cheng3100/wifi_extension_touch_screen/doc/pic/real_effect_2.png

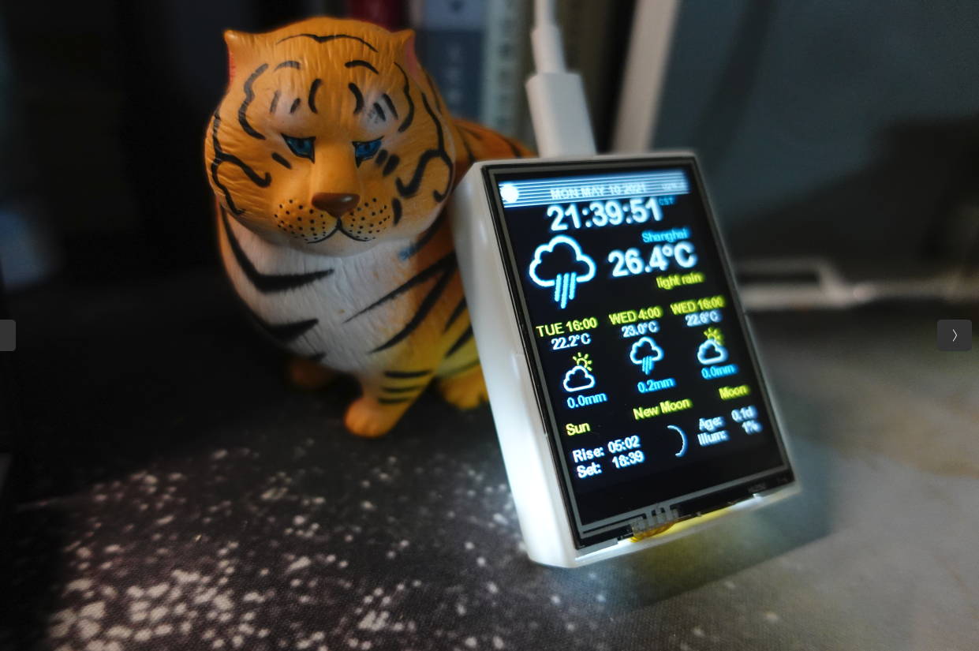
doc/pic/real_effect_2.png
