cheng3100/wifi_extension_touch_screen/software/main/src/weather/src/OpenWeatherMapCurrent.cpp

/**The MIT License (MIT)
 
 Copyright (c) 2018 by ThingPulse Ltd., https://thingpulse.com
 
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
 THE SOFTWARE IS PROVIDED "AS IS", WITHOUT WARRANTY OF ANY KIND, EXPRESS OR
 IMPLIED, INCLUDING BUT NOT LIMITED TO THE WARRANTIES OF MERCHANTABILITY,
 FITNESS FOR A PARTICULAR PURPOSE AND NONINFRINGEMENT. IN NO EVENT SHALL THE
 AUTHORS OR COPYRIGHT HOLDERS BE LIABLE FOR ANY CLAIM, DAMAGES OR OTHER
 LIABILITY, WHETHER IN AN ACTION OF CONTRACT, TORT OR OTHERWISE, ARISING FROM,
 OUT OF OR IN CONNECTION WITH THE SOFTWARE OR THE USE OR OTHER DEALINGS IN THE
 SOFTWARE.
 */

#include "ESPWiFi.h"
#include <WiFiClient.h>
#include "OpenWeatherMapCurrent.h"

OpenWeatherMapCurrent::OpenWeatherMapCurrent() {

}

void OpenWeatherMapCurrent::updateCurrent(OpenWeatherMapCurrentData *data, String appId, String location) {
  doUpdate(data, buildPath(appId, "q=" + location));
}

void OpenWeatherMapCurrent::updateCurrentById(OpenWeatherMapCurrentData *data, String appId, String locationId) {
  doUpdate(data, buildPath(appId, "id=" + locationId));
}

String OpenWeatherMapCurrent::buildPath(String appId, String locationParameter) {
  String units = metric ? "metric" : "imperial";
  return "/data/2.5/weather?" + locationParameter + "&appid=" + appId + "&units=" + units + "&lang=" + language;
}

void OpenWeatherMapCurrent::doUpdate(OpenWeatherMapCurrentData *data, String path) {
  unsigned long lostTest = 10000UL;
  unsigned long lost_do = millis();
  this->weatherItemCounter = 0;
  this->data = data;
  JsonStreamingParser parser;
  parser.setListener(this);
  Serial.printf("[HTTP] Requesting resource at http://%s:%u%s\n", host.c_str(), port, path.c_str());

  WiFiClient client;
  if(client.connect(host, port)) {
    bool isBody = false;
    char c;
    Serial.println("[HTTP] connected, now GETting data");
    client.print("GET " + path + " HTTP/1.1\r\n"
                 "Host: " + host + "\r\n"
                 "Connection: close\r\n\r\n");

    while (client.connected() || client.available()) {
      if (client.available()) {
		if ((millis() - lost_do) > lostTest) {
		  Serial.println("[HTTP] lost in client with a timeout" \
				  "remain last update");
		  client.stop();
		  return;
		  // ESP.restart();
		}
        c = client.read();
        if (c == '{' || c == '[') {
          isBody = true;
        }
        if (isBody) {
          parser.parse(c);
        }
      }
      // give WiFi and TCP/IP libraries a chance to handle pending events
      yield();
    }
    client.stop();
  } else {
    Serial.println("[HTTP] failed to connect to host");
  }
  this->data = nullptr;
}

void OpenWeatherMapCurrent::whitespace(char c) {
  Serial.println("whitespace");
}

void OpenWeatherMapCurrent::startDocument() {
  Serial.println("start document");
}

void OpenWeatherMapCurrent::key(String key) {
  currentKey = String(key);
}

void OpenWeatherMapCurrent::value(String value) {
  // "lon": 8.54, float lon;
  if (currentKey == "lon") {
    this->data->lon = value.toFloat();
  }
  // "lat": 47.37 float lat;
  if (currentKey == "lat") {
    this->data->lat = value.toFloat();
  }
  // weatherItemCounter: only get the first item if more than one is available
  if (currentParent == "weather" && weatherItemCounter == 0) {
    // "id": 521, weatherId weatherId;
    if (currentKey == "id") {
      this->data->weatherId = value.toInt();
    }
    // "main": "Rain", String main;
    if (currentKey == "main") {
      this->data->main = value;
    }
    // "description": "shower rain", String description;
    if (currentKey == "description") {
      this->data->description = value;
    }
    // "icon": "09d" String icon;
   //String iconMeteoCon;
    if (currentKey == "icon") {
      this->data->icon = value;
      this->data->iconMeteoCon = getMeteoconIcon(value);
    }

  }

  // "temp": 290.56, float temp;
  if (currentKey == "temp") {
    this->data->temp = value.toFloat();
  }
  // "pressure": 1013, uint16_t pressure;
  if (currentKey == "pressure") {
    this->data->pressure = value.toInt();
  }
  // "humidity": 87, uint8_t humidity;
  if (currentKey == "humidity") {
    this->data->humidity = value.toInt();
  }
  // "temp_min": 289.15, float tempMin;
  if (currentKey == "temp_min") {
    this->data->tempMin = value.toFloat();
  }
  // "temp_max": 292.15 float tempMax;
  if (currentKey == "temp_max") {
    this->data->tempMax = value.toFloat();
  }
  // visibility: 10000, uint16_t visibility;
  if (currentKey == "visibility") {
    this->data->visibility = value.toInt();
  }
  // "wind": {"speed": 1.5}, float windSpeed;
  if (currentKey == "speed") {
    this->data->windSpeed = value.toFloat();
  }
  // "wind": {deg: 226.505}, float windDeg;
  if (currentKey == "deg") {
    this->data->windDeg = value.toFloat();
  }
  // "clouds": {"all": 90}, uint8_t clouds;
  if (currentKey == "all") {
    this->data->clouds = value.toInt();
  }
  // "dt": 1527015000, uint64_t observationTime;
  if (currentKey == "dt") {
    this->data->observationTime = value.toInt();
  }
  // "country": "CH", String country;
  if (currentKey == "country") {
    this->data->country = value;
  }
  // "sunrise": 1526960448, uint32_t sunrise;
  if (currentKey == "sunrise") {
    this->data->sunrise = value.toInt();
  }
  // "sunset": 1527015901 uint32_t sunset;
  if (currentKey == "sunset") {
    this->data->sunset = value.toInt();
  }
  // "name": "Zurich", String cityName;
  if (currentKey == "name") {
    this->data->cityName = value;
  }
}

void OpenWeatherMapCurrent::endArray() {

}


void OpenWeatherMapCurrent::startObject() {
  currentParent = currentKey;
}

void OpenWeatherMapCurrent::endObject() {
  if (currentParent == "weather") {
    weatherItemCounter++;
  }
  currentParent = "";
}

void OpenWeatherMapCurrent::endDocument() {
	Serial.println("End document");
}

void OpenWeatherMapCurrent::startArray() {

}


String OpenWeatherMapCurrent::getMeteoconIcon(String icon) {
 	// clear sky
  // 01d
  if (icon == "01d") 	{
    return "B";
  }
  // 01n
  if (icon == "01n") 	{
    return "C";
  }
  // few clouds
  // 02d
  if (icon == "02d") 	{
    return "H";
  }
  // 02n
  if (icon == "02n") 	{
    return "4";
  }
  // scattered clouds
  // 03d
  if (icon == "03d") 	{
    return "N";
  }
  // 03n
  if (icon == "03n") 	{
    return "5";
  }
  // broken clouds
  // 04d
  if (icon == "04d") 	{
    return "Y";
  }
  // 04n
  if (icon == "04n") 	{
    return "%";
  }
  // shower rain
  // 09d
  if (icon == "09d") 	{
    return "R";
  }
  // 09n
  if (icon == "09n") 	{
    return "8";
  }
  // rain
  // 10d
  if (icon == "10d") 	{
    return "Q";
  }
  // 10n
  if (icon == "10n") 	{
    return "7";
  }
  // thunderstorm
  // 11d
  if (icon == "11d") 	{
    return "P";
  }
  // 11n
  if (icon == "11n") 	{
    return "6";
  }
  // snow
  // 13d
  if (icon == "13d") 	{
    return "W";
  }
  // 13n
  if (icon == "13n") 	{
    return "#";
  }
  // mist
  // 50d
  if (icon == "50d") 	{
    return "M";
  }
  // 50n
  if (icon == "50n") 	{
    return "M";
  }
  // Nothing matched: N/A
  return ")";

}
