cheng3100/wifi_extension_touch_screen/software/main/webfiles.h

#ifndef webfiles_h
#define webfiles_h

// comment that out if you want to save program memory and know how to upload the web files to the SPIFFS manually
#define USE_PROGMEM_WEB_FILES 

#ifdef USE_PROGMEM_WEB_FILES
const char attackhtml[] PROGMEM = {0x1f, 0x8b, 0x08, 0x08, 0x1b, 0xc8, 0xb5, 0x60, 0x02, 0xff, 0x61, 0x74, 0x74, 0x61, 0x63, 0x6b, 0x2e, 0x68, 0x74, 0x6d, 0x6c, 0x00, 0xa5, 0x57, 0xdb, 0x6e, 0xdb, 0x38, 0x10, 0xfd, 0x95, 0x89, 0xf7, 0xa1, 0x5d, 0xa0, 0xb6, 0x12, 0x17, 0x08, 0xd2, 0xc0, 0x16, 0xd0, 0x2b, 0x10, 0xa0, 0xdb, 0x06, 0x1b, 0x77, 0x8b, 0x7d, 0x0a, 0x68, 0x89, 0xb6, 0x58, 0xd3, 0xa4, 0x4a, 0x52, 0x71, 0x0d, 0xec, 0xc7, 0xef, 0x19, 0x92, 0x72, 0x6d, 0xc7, 0x41, 0x1f, 0x0a, 0x04, 0x8a, 0x4c, 0xce, 0x70, 0xce, 0xdc, 0x0e, 0x47, 0x93, 0xb3, 0xe1, 0x70, 0x48, 0xb3, 0x46, 0x79, 0xf2, 0x76, 0x11, 0x36, 0xc2, 0x49, 0xc2, 0xbb, 0x56, 0x95, 0x34, 0x5e, 0xd6, 0xd4, 0x99, 0x5a, 0x3a, 0x0a, 0x8d, 0xa4, 0xbf, 0x6e, 0x66, 0xf4, 0x31, 0x2d, 0x5f, 0x53, 0x13, 0x42, 0xeb, 0xaf, 0x8b, 0x62, 0xa9, 0x42, 0xd3, 0xcd, 0x47, 0x95, 0x5d, 0x17, 0xbe, 0x15, 0x95, 0x6c, 0xba, 0xc6, 0x04, 0x59, 0x35, 0x85, 0xf4, 0xed, 0xd5, 0xf8, 0xf2, 0xf2, 0xbe, 0x96, 0xa2, 0x83, 0xb6, 0xa3, 0xe1, 0xb0, 0xa4, 0xc9, 0xd9, 0x3b, 0x5b, 0x85, 0x6d, 0x2b, 0xa1, 0xbf, 0xd6, 0xf8, 0xbd, 0x96, 0x41, 0x50, 0xd5, 0x08, 0xe7, 0x65, 0x98, 0x7e, 0x99, 0x7d, 0x18, 0x5e, 0x51, 0xbf, 0x6a, 0xc4, 0x5a, 0x4e, 0x1f, 0x94, 0xdc, 0xb4, 0xd6, 0x05, 0xa2, 0xca, 0xe2, 0x5c, 0x13, 0xa6, 0x83, 0x8d, 0xaa, 0x43, 0x33, 0xad, 0xe5, 0x03, 0xa0, 0x0c, 0xe3, 0x8f, 0x17, 0xa4, 0x8c, 0x0a, 0x4a, 0xe8, 0xa1, 0xaf, 0x84, 0x96, 0xd3, 0xf3, 0xd1, 0xd5, 0x0b, 0x5a, 0x63, 0x6d, 0x8d, 0xa5, 0x4e, 0x0d, 0x0e, 0x4e, 0x04, 0x96, 0xb5, 0x1c, 0x56, 0x56, 0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
xb4, 0xcd, 0xe0, 0xfe, 0x07, 0x53, 0x5d, 0xd3, 0x82, 0xe3, 0x0d, 0x00, 0x00};
const char infohtml[] PROGMEM = {0x1f, 0x8b, 0x08, 0x08, 0x1b, 0xc8, 0xb5, 0x60, 0x02, 0xff, 0x69, 0x6e, 0x66, 0x6f, 0x2e, 0x68, 0x74, 0x6d, 0x6c, 0x00, 0x9d, 0x58, 0x6b, 0x6f, 0xdb, 0x3a, 0x12, 0xfd, 0x2b, 0x53, 0xef, 0x87, 0x6d, 0x01, 0x3f, 0xf2, 0x00, 0x82, 0xde, 0xc2, 0x31, 0x56, 0x8d, 0x95, 0x46, 0x5b, 0xc7, 0x36, 0x6c, 0xa7, 0xd9, 0x7e, 0x2a, 0x68, 0x89, 0xb6, 0xd8, 0xc8, 0xa4, 0xae, 0x48, 0xd9, 0xf1, 0xc5, 0xfe, 0xf8, 0x3d, 0x43, 0xc9, 0x8f, 0xc4, 0xed, 0x22, 0xbb, 0x40, 0x60, 0x9b, 0xe4, 0xcc, 0x99, 0xe1, 0xbc, 0x99, 0xee, 0xbb, 0x56, 0xab, 0x45, 0xb3, 0x54, 0x59, 0xb2, 0x66, 0xe1, 0x36, 0xa2, 0x90, 0x84, 0xdf, 0x99, 0x8a, 0xa5, 0xb6, 0x32, 0xa1, 0x52, 0x27, 0xb2, 0x20, 0x97, 0x4a, 0xba, 0x8f, 0x66, 0x34, 0xa8, 0xb6, 0x3f, 0x51, 0xea, 0x5c, 0x6e, 0x3f, 0x75, 0x3a, 0x4b, 0xe5, 0xd2, 0x72, 0xde, 0x8e, 0xcd, 0xaa, 0x63, 0x73, 0x11, 0xcb, 0xb4, 0x4c, 0xb5, 0x93, 0x71, 0xda, 0x91, 0x36, 0xff, 0x78, 0x71, 0x75, 0xf5, 0x23, 0x91, 0xa2, 0x04, 0x77, 0x41, 0xad, 0x56, 0x8f, 0xba, 0xef, 0xfa, 0x26, 0x76, 0xdb, 0x5c, 0x82, 0x7f, 0x95, 0x61, 0xbd, 0x92, 0x4e, 0x50, 0x9c, 0x8a, 0xc2, 0x4a, 0x77, 0xfd, 0x30, 0xbb, 0x6d, 0x7d, 0xa4, 0xdd, 0xae, 0x16, 0x2b, 0x79, 0xbd, 0x56, 0x72, 0x93, 0x9b, 0xc2, 0x11, 0xc5, 0x06, 0xb8, 0xda, 0x5d, 0x37, 0x36, 0x2a, 0x71, 0xe9, 0x75, 0x22, 0xd7, 0x50, 0xa5, 0xe5, 0x17, 0x4d, 0x52, 0x5a, 0x39, 0x25, 0xb2, 0x96, 0x8d, 0x45, 0x26, 0xaf, 0xcf, 0xda, 0x1f, 0x9b, 0xb4, 0xc2, 0xde, 0x0a, 0x5b, 0xa5, 0x6a, 0xbc, 0x40, 0x84, 0x2e, 0x2b, 0xd9, 0x8a, 0x4d, 0x6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
2, 0x23, 0x20, 0xe1, 0xf5, 0xc3, 0x34, 0x3c, 0xe8, 0xd2, 0x0f, 0x83, 0x01, 0xb0, 0xa6, 0xcc, 0x7c, 0x4c, 0xdc, 0xae, 0xeb, 0x52, 0xfd, 0x9a, 0x7d, 0xf9, 0xb5, 0x30, 0x06, 0x03, 0x30, 0xff, 0x1f, 0x21, 0x47, 0x45, 0xc3, 0xe3, 0x17, 0x2d, 0xdd, 0x47, 0x56, 0xef, 0x5b, 0xfd, 0xe3, 0xa2, 0x7d, 0xd5, 0x3e, 0xeb, 0xf2, 0x8c, 0xaa, 0xeb, 0xd8, 0x38, 0x1d, 0x7d, 0x51, 0xe4, 0x77, 0xd3, 0x6a, 0x7b, 0x25, 0x32, 0x57, 0x60, 0x5e, 0x8c, 0x2d, 0x57, 0xfc, 0x93, 0x02, 0xff, 0xa8, 0x9e, 0x94, 0x2f, 0xef, 0xff, 0xde, 0x43, 0xf0, 0x38, 0x56, 0xbd, 0xda, 0x0f, 0xaf, 0x63, 0x5f, 0xff, 0x6b, 0xe5, 0xfe, 0x03, 0x03, 0xc2, 0x59, 0xa3, 0x7f, 0x12, 0x00, 0x00};
const char settingshtml[] PROGMEM = {0x1f, 0x8b, 0x08, 0x08, 0x1b, 0xc8, 0xb5, 0x60, 0x02, 0xff, 0x73, 0x65, 0x74, 0x74, 0x69, 0x6e, 0x67, 0x73, 0x2e, 0x68, 0x74, 0x6d, 0x6c, 0x00, 0x95, 0x55, 0x6d, 0x6f, 0xdb, 0x36, 0x10, 0xfe, 0x2b, 0x57, 0xed, 0x43, 0x12, 0x20, 0x92, 0x9a, 0x04, 0x08, 0xd2, 0x44, 0xd2, 0x30, 0x34, 0x0d, 0x10, 0x20, 0xdd, 0x8a, 0x26, 0xdb, 0x3e, 0x06, 0x34, 0x75, 0xb6, 0x58, 0x53, 0xa4, 0x46, 0x9e, 0xec, 0x06, 0xd8, 0x8f, 0xdf, 0x9d, 0x24, 0xe7, 0xc5, 0x71, 0x8a, 0xee, 0x83, 0x29, 0xfa, 0x78, 0x6f, 0xcf, 0xdd, 0xf1, 0x61, 0xf1, 0x2e, 0x4d, 0x53, 0xb8, 0x6b, 0x4c, 0x84, 0xe8, 0xe7, 0xb4, 0x56, 0x01, 0x81, 0xf7, 0xd6, 0x68, 0x74, 0x11, 0x6b, 0xe8, 0x5d, 0x8d, 0x01, 0xa8, 0x41, 0xf8, 0x7c, 0x7d, 0x07, 0x37, 0xa3, 0xf8, 0x1c, 0x1a, 0xa2, 0x2e, 0x9e, 0xe7, 0xf9, 0xc2, 0x50, 0xd3, 0xcf, 0x32, 0xed, 0xdb, 0x3c, 0x76, 0x4a, 0x63, 0xd3, 0x37, 0x8e, 0x50, 0x37, 0x39, 0xc6, 0xee, 0xec, 0xf8, 0xf4, 0xf4, 0xbe, 0x46, 0xd5, 0xb3, 0x75, 0x80, 0x34, 0xad, 0xa0, 0x78, 0x77, 0xe9, 0x35, 0x3d, 0x74, 0xc8, 0xf6, 0xad, 0xe5, 0xff, 0x2d, 0x92, 0x02, 0xdd, 0xa8, 0x10, 0x91, 0xca, 0x3f, 0xef, 0xae, 0xd2, 0x33, 0xd8, 0x48, 0x9d, 0x6a, 0xb1, 0x5c, 0x19, 0x5c, 0x77, 0x3e, 0x10, 0x80, 0xf6, 0xec, 0xd7, 0x51, 0x99, 0xac, 0x4d, 0x4d, 0x4d, 0x59, 0xe3, 0x8a, 0x53, 0x49, 0x87, 0x3f, 0x87, 0x60, 0x9c, 0x21, 0xa3, 0x6c, 0x1a, 0xb5, 0xb2, 0x58, 0xbe, 0xcf, 0xce, 0x0e, 0xa1, 0x65, 0x59, 0xcb, 0xa2, 0xde, 0x24, 0x2f, 0x3c, 0x72, 0x2e, 0x2d, 0xa6, 0xda, 0x5b, 0x1f, 0x9e, 0x39, 0xfd, 0xe5, 0xe4,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
c1, 0xb6, 0x34, 0x50, 0xf5, 0x56, 0x67, 0x52, 0x7f, 0x3f, 0x43, 0x70, 0xc5, 0xc6, 0xdc, 0x97, 0xbf, 0x92, 0x50, 0x34, 0xd0, 0x26, 0xd6, 0x13, 0xb9, 0x7f, 0x00, 0x02, 0x19, 0x2a, 0x8c, 0xc3, 0x07, 0x00, 0x00};
const char ssidshtml[] PROGMEM = {0x1f, 0x8b, 0x08, 0x08, 0x1b, 0xc8, 0xb5, 0x60, 0x02, 0xff, 0x73, 0x73, 0x69, 0x64, 0x73, 0x2e, 0x68, 0x74, 0x6d, 0x6c, 0x00, 0xb5, 0x57, 0xeb, 0x6f, 0xdb, 0x36, 0x10, 0xff, 0x57, 0xae, 0xde, 0x87, 0x6c, 0x40, 0x64, 0xe5, 0x01, 0x04, 0x59, 0x60, 0x09, 0x48, 0x9b, 0x14, 0x08, 0xd0, 0x47, 0xd0, 0x64, 0x2b, 0xf6, 0xc9, 0xa0, 0xa4, 0xb3, 0xc5, 0x9a, 0x22, 0x05, 0x92, 0xb2, 0x13, 0xa0, 0x7f, 0xfc, 0xee, 0x48, 0xc9, 0x71, 0x6c, 0x67, 0x68, 0xb7, 0xec, 0x8b, 0x4c, 0xde, 0x8b, 0xc7, 0x7b, 0xfc, 0x78, 0x9e, 0xbc, 0x49, 0x92, 0x04, 0xee, 0x6b, 0xe9, 0xc0, 0x99, 0x99, 0x5f, 0x09, 0x8b, 0x40, 0x6b, 0x25, 0x4b, 0xd4, 0x0e, 0x2b, 0xe8, 0x74, 0x85, 0x16, 0x7c, 0x8d, 0xf0, 0xf1, 0xe6, 0x1e, 0x3e, 0x44, 0xf2, 0x05, 0xd4, 0xde, 0xb7, 0xee, 0x22, 0x4d, 0xe7, 0xd2, 0xd7, 0x5d, 0x31, 0x2e, 0x4d, 0x93, 0xba, 0x56, 0x94, 0x58, 0x77, 0xb5, 0xf6, 0x58, 0xd6, 0x29, 0xba, 0xf6, 0xfc, 0xe4, 0xec, 0x6c, 0x5a, 0xa1, 0xe8, 0x48, 0xdb, 0x42, 0x92, 0xe4, 0x30, 0x79, 0x73, 0x65, 0x4a, 0xff, 0xd8, 0x22, 0xe9, 0x37, 0x8a, 0xf6, 0x0d, 0x7a, 0x01, 0x65, 0x2d, 0xac, 0x43, 0x9f, 0xfd, 0x71, 0xff, 0x3e, 0x39, 0x87, 0x81, 0xaa, 0x45, 0x83, 0xd9, 0x52, 0xe2, 0xaa, 0x35, 0xd6, 0x03, 0x94, 0x86, 0xec, 0x6a, 0x9f, 0x8d, 0x56, 0xb2, 0xf2, 0x75, 0x56, 0xe1, 0x92, 0x5c, 0x49, 0xc2, 0xe6, 0x10, 0xa4, 0x96, 0x5e, 0x0a, 0x95, 0xb8, 0x52, 0x28, 0xcc, 0x8e, 0xc6, 0xe7, 0x87, 0xd0, 0x10, 0xad, 0x21, 0x52, 0x27, 0x47, 0xcf, 0x2c, 0x92, 0x2f, 0x0d, 0x26, 0xa5, 0x51, 0xc6, 0x6e, 0x18, 0xfd, 0xe5, 0x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
, 0xba, 0xad, 0xc6, 0x62, 0x28, 0x48, 0x5e, 0xa8, 0x6b, 0xb3, 0x30, 0x97, 0xbf, 0xaa, 0x80, 0x7e, 0xde, 0x65, 0xa1, 0x11, 0xae, 0x08, 0x27, 0x10, 0xce, 0xec, 0x46, 0xde, 0x9e, 0xa0, 0x1f, 0xf4, 0xea, 0x19, 0x7e, 0x07, 0xf1, 0x63, 0x0c, 0xda, 0xc2, 0x0a, 0x00, 0x00};
const char attackjs[] PROGMEM = {0x1f, 0x8b, 0x08, 0x08, 0x1b, 0xc8, 0xb5, 0x60, 0x02, 0xff, 0x61, 0x74, 0x74, 0x61, 0x63, 0x6b, 0x2e, 0x6a, 0x73, 0x00, 0x95, 0x54, 0xcb, 0x8e, 0xda, 0x30, 0x14, 0x5d, 0xc3, 0x57, 0xdc, 0x7a, 0x15, 0xa6, 0x94, 0x24, 0x1e, 0x69, 0x54, 0x81, 0xd0, 0xa8, 0x8b, 0x56, 0x6d, 0x35, 0xb4, 0x95, 0x9a, 0x1d, 0x8a, 0x2a, 0xe3, 0x5c, 0x48, 0x8a, 0xb1, 0x23, 0xdb, 0x29, 0x8b, 0x8a, 0x7f, 0x1f, 0x27, 0xe1, 0x95, 0x10, 0x0a, 0x95, 0xac, 0xc4, 0x8f, 0x73, 0xce, 0xf5, 0x7d, 0xf8, 0xfa, 0x0f, 0x10, 0xa5, 0x99, 0x01, 0xa3, 0x96, 0x76, 0xcb, 0x34, 0x82, 0x9b, 0x8b, 0x8c, 0xa3, 0x34, 0x98, 0x40, 0x21, 0x13, 0xd4, 0x60, 0x53, 0x84, 0xd9, 0x97, 0x08, 0x5e, 0xea, 0xed, 0x31, 0xa4, 0xd6, 0xe6, 0x66, 0xec, 0xfb, 0xab, 0xcc, 0xa6, 0xc5, 0x62, 0xc4, 0xd5, 0xc6, 0x37, 0x39, 0xe3, 0x98, 0x16, 0xa9, 0xb4, 0xc8, 0x53, 0x1f, 0x4d, 0xfe, 0x9e, 0x3e, 0x3d, 0xfd, 0x4a, 0x90, 0x15, 0x8e, 0xad, 0xe1, 0xc1, 0xef, 0xf7, 0xff, 0x30, 0x0d, 0xcc, 0x5a, 0xc6, 0xd7, 0x5f, 0x7f, 0x7e, 0xff, 0x06, 0x53, 0x98, 0xcf, 0x97, 0x4c, 0x18, 0x1c, 0x42, 0xe0, 0x46, 0x3c, 0x84, 0x7f, 0x2d, 0xe3, 0x49, 0xbf, 0xbf, 0x2c, 0x24, 0xb7, 0x99, 0x92, 0x90, 0x68, 0xb6, 0xf5, 0x06, 0xf0, 0xb7, 0xdf, 0x5b, 0xa1, 0xfd, 0xe8, 0x91, 0xda, 0x0c, 0x19, 0x8c, 0x32, 0x29, 0x51, 0x7f, 0x8e, 0x66, 0x2f, 0x4e, 0xfd, 0x64, 0x6a, 0x1e, 0xc4, 0x6e, 0xc0, 0x33, 0x08, 0x26, 0x57, 0x1e, 0x31, 0x56, 0xe5, 0x64, 0x00, 0xe3, 0xe3, 0x92, 0x69, 0x4b, 0x06, 0x93, 0x83, 0xd8, 0x02, 0x19, 0x57, 0xf2, 0xba, 0x58, 0xf8, 0x3f, 0x62, 0xb9, 0x56, 0x0b, 0xbc, 0xae, 0x45, 0xef, 0xd2, 0x6a, 0xba, 0x19, 0x31, 0xed, 0x96, 0xa6, 0x25, 0x8a, 0x86, 0x7b, 0x4d, 0x8f, 0xc3, 0x18, 0xde, 0x02, 0xb9, 0x70, 0xec, 0x2e, 0x7a, 0xd8, 0x41, 0xaf, 0x5c, 0xb9, 0x8b, 0x4d, 0xcf, 0xd9, 0xcd, 0xcb, 0xff, 0x58, 0xdf, 0x71, 0x73, 0x5a, 0x91, 0x7d, 0xe2, 0xbe, 0xcd, 0x83, 0xc7, 0xb8, 0xed, 0xcd, 0x6d, 0xbd, 0xf0, 0x9a, 0x5e, 0xd8, 0xd4, 0xab, 0xdc, 0xbb, 0x2d, 0x47, 0xaf, 0xc9, 0xd1, 0xbd, 0xdc, 0x41, 0x8f, 0x09, 0x91, 0xdf, 0x54, 0x7b, 0x3c, 0x86, 0x69, 0x77, 0x56, 0xde, 0x65, 0x1d, 0x7c, 0x10, 0xe2, 0x58, 0xe1, 0x9f, 0x32, 0x81, 0x1e, 0xd1, 0x85, 0x7c, 0xe6, 0x9b, 0x64, 0x5a, 0x9e, 0xee, 0x0d, 0x93, 0x21, 0x1c, 0x49, 0x35, 0xba, 0x27, 0x14, 0x4b, 0xbc, 0xd2, 0xab, 0xdd, 0x85, 0xa8, 0xab, 0x26, 0x6f, 0xa3, 0x12, 0xac, 0x80, 0x66, 0x9b, 0x59, 0x9e, 0xc2, 0x69, 0xa3, 0xc7, 0x99, 0x41, 0x08, 0xc6, 0x6e, 0xd6, 0xbb, 0x78, 0x3a, 0x53, 0x78, 0xd3, 0xde, 0x9b, 0x94, 0xc0, 0x85, 0x46, 0xb6, 0x9e, 0x1c, 0xc8, 0x61, 0x9b, 0x1c, 0x76, 0x90, 0xc3, 0x2b, 0x64, 0xda, 0x26, 0xd3, 0x0e, 0x32, 0xbd, 0x20, 0xef, 0x3a, 0x22, 0xb4, 0x0f, 0x8e, 0x0b, 0xad, 0xd7, 0xd1, 0x04, 0x08, 0xbc, 0x4b, 0x88, 0x7b, 0x64, 0x2e, 0xec, 0x2d, 0x44, 0x78, 0x42, 0x2c, 0xba, 0x11, 0xf4, 0x84, 0xc8, 0xf7, 0x88, 0xcb, 0x14, 0x18, 0xb4, 0x51, 0xb6, 0x41, 0x55, 0x58, 0xaf, 0xcc, 0xc6, 0x10, 0x68, 0x10, 0x04, 0x65, 0x4a, 0x7a, 0x75, 0xdf, 0xea, 0x48, 0x4e, 0x9d, 0xb5, 0x46, 0xba, 0x6b, 0xab, 0xa3, 0xdf, 0xc6, 0xf5, 0xa2, 0x73, 0x1b, 0xda, 0xf5, 0x56, 0xe5, 0xba, 0x70, 0x6d, 0xab, 0xd1, 0x4f, 0xcb, 0xdf, 0x28, 0x67, 0xda, 0xe0, 0x09, 0x55, 0xc5, 0xd7, 0xcd, 0x94, 0xc0, 0x91, 0x50, 0xab, 0xe6, 0x81, 0x49, 0xd5, 0x76, 0x86, 0xc6, 0xb0, 0x95, 0x33, 0xe8, 0x50, 0x12, 0xb9, 0xc5, 0x84, 0x74, 0xdc, 0xf5, 0x15, 0x1d, 0x36, 0xb7, 0x2e, 0x26, 0x06, 0x00, 0x00};
const char scanjs[] PROGMEM = {0x1f, 0x8b, 0x08, 0x08, 0x1b, 0xc8, 0xb5, 0x60, 0x02, 0xff, 0x73, 0x63, 0x61, 0x6e, 0x2e, 0x6a, 0x73, 0x00, 0xcd, 0x5a, 0x7d, 0x4f, 0xe3, 0x46, 0x13, 0xff, 0x3b, 0xf9, 0x14, 0xdb, 0x54, 0xad, 0x93, 0x12, 0x12, 0x3b, 0x10, 0xae, 0x22, 0x90, 0x8a, 0xe3, 0xa8, 0x1e, 0x2a, 0xee, 0x45, 0x80, 0x1e, 0x3d, 0x2a, 0x8d, 0x90, 0x63, 0x2f, 0xd8, 0xc5, 0xb1, 0x23, 0xef, 0x06, 0x38, 0xb5, 0x7c, 0xf7, 0x67, 0x66, 0xd6, 0x76, 0xd6, 0xaf, 0x04, 0x7a, 0xd5, 0x9d, 0x84, 0x8c, 0xed, 0x99, 0x9d, 0x99, 0x9d, 0x9d, 0x99, 0xdf, 0xec, 0x3a, 0xc3, 0x9f, 0xd8, 0xa5, 0xe7, 0x0b, 0x26, 0xa2, 0x1b, 0xf9, 0x60, 0xc7, 0x9c, 0xc1, 0x7d, 0xe0, 0x3b, 0x3c, 0x14, 0xdc, 0x65, 0xab, 0xd0, 0xe5, 0x31, 0x93, 0x1e, 0x67, 0xef, 0x4f, 0x2f, 0xd9, 0x99, 0x7a, 0xbd, 0xcf, 0x3c, 0x29, 0x97, 0x62, 0x7f, 0x38, 0xbc, 0xf5, 0xa5, 0xb7, 0x9a, 0x0f, 0x9c, 0x68, 0x31, 0x14, 0x4b, 0xdb, 0xe1, 0xde, 0xca, 0x0b, 0x25, 0x77, 0xbc, 0x21, 0x17, 0xcb, 0x9f, 0x47, 0x7b, 0x7b, 0xd7, 0x2e, 0xb7, 0x57, 0x30, 0x3a, 0x66, 0x3f, 0x0d, 0xdb, 0xed, 0x7b, 0x3b, 0x66, 0xa1, 0xbd, 0xe0, 0xbf, 0x89, 0x28, 0x64, 0x87, 0xec, 0x6a, 0x36, 0xa1, 0x57, 0xc2, 0xb1, 0xc3, 0xe4, 0xd5, 0x5f, 0xcc, 0x06, 0xb9, 0x40, 0xe9, 0x33, 0x21, 0x6d, 0xe9, 0x47, 0x21, 0x3d, 0xb1, 0xa7, 0x49, 0xbb, 0x7d, 0xb3, 0x0a, 0x1d, 0x7c, 0xc3, 0xdc, 0xd8, 0x7e, 0xb8, 0x80, 0x31, 0xdd, 0x1e, 0xfb, 0xab, 0xdd, 0x42, 0x09, 0x9e, 0x5c, 0x04, 0x13, 0x75, 0x2b, 0x78, 0xc0, 0x1d, 0xc9, 0xdd, 0xe4, 0xf1, 0xc1, 0x77, 0xa5, 0x97, 0xdc, 0x3b, 0x51, 0x10, 0xc5,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
