cheng3100/wifi_extension_touch_screen/software/main/ArialRounded.h

// Created by http://oleddisplay.squix.ch/ Consider a donation
// In case of problems make sure that you are using the font file with the correct version!
const char ArialRoundedMTBold_14[] PROGMEM = {
  0x0E, // Width: 14
  0x11, // Height: 17
  0x20, // First Char: 32 
  0xE0, // Numbers of Chars: 224

  // Jump Table:
  0xFF, 0xFF, 0x00, 0x04,  // 32:65535
  0x00, 0x00, 0x08, 0x05,  // 33:0
  0x00, 0x08, 0x10, 0x07,  // 34:8
  0x00, 0x18, 0x17, 0x08,  // 35:24
  0x00, 0x2F, 0x17, 0x08,  // 36:47
  0x00, 0x46, 0x23, 0x0C,  // 37:70
  0x00, 0x69, 0x20, 0x0B,  // 38:105
  0x00, 0x89, 0x07, 0x03,  // 39:137
  0x00, 0x90, 0x0F, 0x05,  // 40:144
  0x00, 0x9F, 0x0B, 0x05,  // 41:159
  0x00, 0xAA, 0x10, 0x06,  // 42:170
  0x00, 0xBA, 0x17, 0x08,  // 43:186
  0x00, 0xD1, 0x08, 0x04,  // 44:209
  0x00, 0xD9, 0x0B, 0x05,  // 45:217
  0x00, 0xE4, 0x08, 0x04,  // 46:228
  0x00, 0xEC, 0x0A, 0x04,  // 47:236
  0x00, 0xF6, 0x17, 0x08,  // 48:246
  0x01, 0x0D, 0x11, 0x08,  // 49:269
  0x01, 0x1E, 0x17, 0x08,  // 50:286
  0x01, 0x35, 0x17, 0x08,  // 51:309
  0x01, 0x4C, 0x17, 0x08,  // 52:332
  0x01, 0x63, 0x17, 0x08,  // 53:355
  0x01, 0x7A, 0x17, 0x08,  // 54:378
  0x01, 0x91, 0x16, 0x08,  // 55:401
  0x01, 0xA7, 0x17, 0x08,  // 56:423
  0x01, 0xBE, 0x17, 0x08,  // 57:446
  0x01, 0xD5, 0x08, 0x04,  // 58:469
  0x01, 0xDD, 0x08, 0x04,  // 59:477
  0x01, 0xE5, 0x17, 0x08,  // 60:485
  0x01, 0xFC, 0x17, 0x08,  // 61:508
  0x02, 0x13, 0x17, 0x08,  // 62:531
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
};
