cheng3100/wifi_extension_touch_screen/software/main/CLI.h

/* This software is licensed under the MIT License: https://github.com/spacehuhntech/esp8266_deauther */

#pragma once

#include "Arduino.h"
#include <ESP8266WiFi.h>
// extern "C" {
//   #include "user_interface.h"
// }
#include "language.h"
#include "A_config.h"
#include "SimpleList.h"
// #include "Names.h"
// #include "SSIDs.h"
// #include "Scan.h"
// #include "Attack.h"
// #include "DisplayUI.h"
// #include "led.h"

// extern Names names;
// extern SSIDs ssids;
// extern Accesspoints accesspoints;
// extern Stations     stations;
// extern Scan   scan;
// extern Attack attack;
// extern DisplayUI displayUI;
// extern uint32_t  currentTime;
// extern uint32_t  autosaveTime;

// extern String macToStr(const uint8_t* mac);
// extern bool strToMac(String macStr, uint8_t* mac);
// extern bool strToIP(String ipStr, uint8_t* ip);
// extern void strToColor(String str, uint8_t* buf);
// extern void readFileToSerial(String path, bool showLineNum);
// extern bool readFile(String path, String& buf);
// extern bool removeFile(String path);
// extern bool copyFile(String pathFrom, String pathTo);
// extern bool renameFile(String pathFrom, String pathTo);
// extern bool appendFile(String path, String& buf);
// extern bool removeLines(String path, int lineFrom, int lineTo);
// extern bool replaceLine(String path, int line, String& buf);
// extern bool equalsKeyword(const char* str, const char* keyword);

class CLI {
    public:
        CLI();
        ~CLI();

        void load();
        void load(String filepath);

        void enable();
        void disable();

        void update();
        void stop();

        void enableDelay(uint32_t delayTime);

        void exec(String input);
        void execFile(String path);
        void runLine(String input);
        void runCommand(String input);

    private:
        bool enabled = false;

        SimpleList<String>* list;
        SimpleList<String>* queue;

        bool delayed            = false;
        uint32_t delayTime      = 0;
        uint32_t delayStartTime = 0;

        String execPath = "/autostart.txt";

        struct Keyword {
            const char* name;
            const char* shortName;
            const char* alt;
        };

        void error(String message);
        void parameterError(String parameter);
        bool isInt(String str);
        int toInt(String str);
        uint32_t getTime(String time);
        bool eqlsCMD(int i, const char* keyword);
};
